Karpova-Lab/cerebro_DBS/Qt/Gambit/mainwindow.h

/*~~~~~~~~~~~~~~~~~~~~~~~~~~~~~~~~~~~~~~~~~~~~~~~~~~~~~~~~~~~~~~~~~~~~~~~~~~~~~~
MIT License

Copyright (c) 2015-2018 Andy S. Lustig

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
THE SOFTWARE IS PROVIDED "AS IS", WITHOUT WARRANTY OF ANY KIND, EXPRESS OR
IMPLIED, INCLUDING BUT NOT LIMITED TO THE WARRANTIES OF MERCHANTABILITY,
FITNESS FOR A PARTICULAR PURPOSE AND NONINFRINGEMENT. IN NO EVENT SHALL THE
AUTHORS OR COPYRIGHT HOLDERS BE LIABLE FOR ANY CLAIM, DAMAGES OR OTHER
LIABILITY, WHETHER IN AN ACTION OF CONTRACT, TORT OR OTHERWISE, ARISING FROM,
OUT OF OR IN CONNECTION WITH THE SOFTWARE OR THE USE OR OTHER DEALINGS IN THE
SOFTWARE.
~~~~~~~~~~~~~~~~~~~~~~~~~~~~~~~~~~~~~~~~~~~~~~~~~~~~~~~~~~~~~~~~~~~~~~~~~~~~~~~*/
#ifndef MAINWINDOW_H
#define MAINWINDOW_H

#include <QMainWindow>
#include <QtWidgets>
#include <QtSerialPort/QSerialPort>
#include <QSerialPortInfo>
#include <qtimer.h>
#include <settingsDialog.h>

class MainWindow : public QMainWindow
{
    Q_OBJECT

protected:
    void closeEvent(QCloseEvent *event);

public:
    MainWindow(QWidget *parent = 0);
    ~MainWindow();

private:

    QString                 usbTag,usbDescription;
    QString                 onTimeString,offTimeString;
    bool                    baseConnected,cerebroConnected;
    bool                    inTestloop;
    int                     testCount;
    bool                    startingUp;
    bool                    debugOn;
    QSerialPort*            serial,*serial2;
    QTimer*                 timer;
    settingsDialog          *settingsDlog;
    bool                    pythonEnabled,mcubeEnabled,showHistogram;
    bool                    errorThrown;
    float                   baseFilter;
    QString                 startTime;
    QString                 saveName1;
    bool                    repeatOn;
    int                     titleLeftPower, titleRightPower;
    QString                 ratNumber,rigNumber;
    QString                 gambitVersion;
    bool                    sessionHasBegun;
    int                     baseChannel;

    //Menus
    QAction*                gotoSettings,*toggleDebug,*openDir,*gotoApplocation,*gotoDocs,*about,*graphResults;
    QMenu*                  fileMenu,*viewMenu,*toolMenu,*goMenu,*helpMenu;
    QMessageBox*            aboutDialog;

    //Experimental Setup
    QGroupBox*              equipmentBox;
    QGridLayout*            equipmentLayout;
    QListWidget*            rigSelect,*ratSelect;
    QComboBox*              serialPortList;
    QLabel*                 connectBS_label,*cerebroNum_lbl;
    QPushButton*            refresh_btn,*connect_btn,*rig_lbl,*rat_lbl;
    QCheckBox*              debugCheckbox;
    QStringList             aliasStringList,rigList,ratList;
    QSpinBox*               cerebroNum_spin;

    //Cerebro Status
    QGroupBox*              cerStatusBox;
    QGridLayout*            cerStatusLayout;
    QLabel*                 implantTitle_lbl,*waveformTitle_lbl,*serialNumber_lbl,*cerFirmware_lbl,
                            *PosAmp_lbl,*NegAmp_lbl,*cerDelay_lbl,*negDur_lbl,*posDur_lbl,*trainDur_lbl,*freq_lbl;
    QPushButton*            getInfo_btn;
    QProgressBar*           batteryIndicator;
    QLabel*                 battery_lbl;

    //Base Station Monitor
    QPushButton*            clearBase_btn;
    QLabel*                 baseFilter_label,*baseChannel_lbl;
    QGridLayout*            serialMonitorLayout;
    QGroupBox*              baseBox;
    QPlainTextEdit*         baseMonitor;
    QPushButton*            saveMonitor_btn;
    QString                 baseBuffer;

    //Cerebro Monitor
    QDialog*                downloaderDialog;
    QPushButton*            refresh2_btn,*connect2_btn,*clearDownload_btn,*channelSendButton,*queryCerebro_btn;
    QGridLayout*            connectionLayout2;
    QComboBox*              serialPortList2;
    QLabel*                 connectLU_label,*download_title,*channelLabel;
    QPlainTextEdit*         cerebroMonitor;
    QSpinBox*               channelSpinBox;

    //Waveform Adjustment
    QGroupBox*              adjustBox;
    QLabel*                 postive_lbl, *negative_lbl,*pulsefreq_lbl,*trainDuration_lbl,*fade_label;
    QDoubleSpinBox*         posAmp_spn,*negAmp_spn,*posDur_spn,*negDur_spn,*trainDuration_spn,*startDelay_spn,*freq_spn;
    QPushButton*            sendSettings_btn;
    QGridLayout*            adjustmentLayout;
    QCheckBox*              startDelay_checkbox;

    //Triggering & Debugging
    QGroupBox*              bugBox;
    QGridLayout*            triggerLayout;
    QCheckBox*              trigger_checkbox;
    QSpinBox*               trials_spn;
    QPushButton*            trigger_btn,*stop_btn,*abort_btn,*batteryStatus_btn,
                            *macro_btn,*cerMonitor_btn,*toggleStim_btn,*stimOff_btn;
    QProgressBar*           testProgress;
    QLineEdit*              macroText;

    //Session Start
    QDialog*                sessionStartDialog;
    QGridLayout*            sessionStartLayout;
    QLabel*                 baseConnected_lbl,*cerebroConnected_lbl,*implantSettingsMatch_lbl,*newCerebro_lbl;
    QPlainTextEdit*         sessionStartMonitor;
    QPushButton*            startSession_btn,*retry_btn,*newCerebro_btn,*setSerial_btn;
    QGridLayout*            mainLayout;
    QSpinBox*               newCerebro_spin;

private slots:

    //Menu functions
    void getGraphs();
    void openDocs();
    void gotoDir();
    void gotoAppLocation();
    void showDebug();
    void setDebug();

    //Connect to ports
    void applySettings();
    void fillBasestationPorts();
    void fillCerebroPorts();
    void connectBasePort();
    void connectCerebroPort();
    void sendTime();
    void matchPowers();
    void startSession();

    //Monitors
    void errorMsg();
    void clearMonitor();
    void clearMonitor2();
    void readFromBase();
    void readFromCerebro();
    void updateFilter();
    void saveFile();
    void getCerebroInfoOverSerial();
    void updateChannel();

    //Debug Commands
    void sendTrigger();
    void abort();
    void macro();
    void getInfo();
    void getBatteryStatus();
    void checkForBase();
    void toggleStim();
    void stimOff();

    //Cerebro Parmeters
    void startDelayChecked();
    void set();
    void setupCerebro();
    void updateSerial();
};


#endif // MAINWINDOW_H
